SteevenRodriguez/AMSTEcIOT/Documentos Entregables/Diagrama de actividades/Diagrama de actividades HU1.png

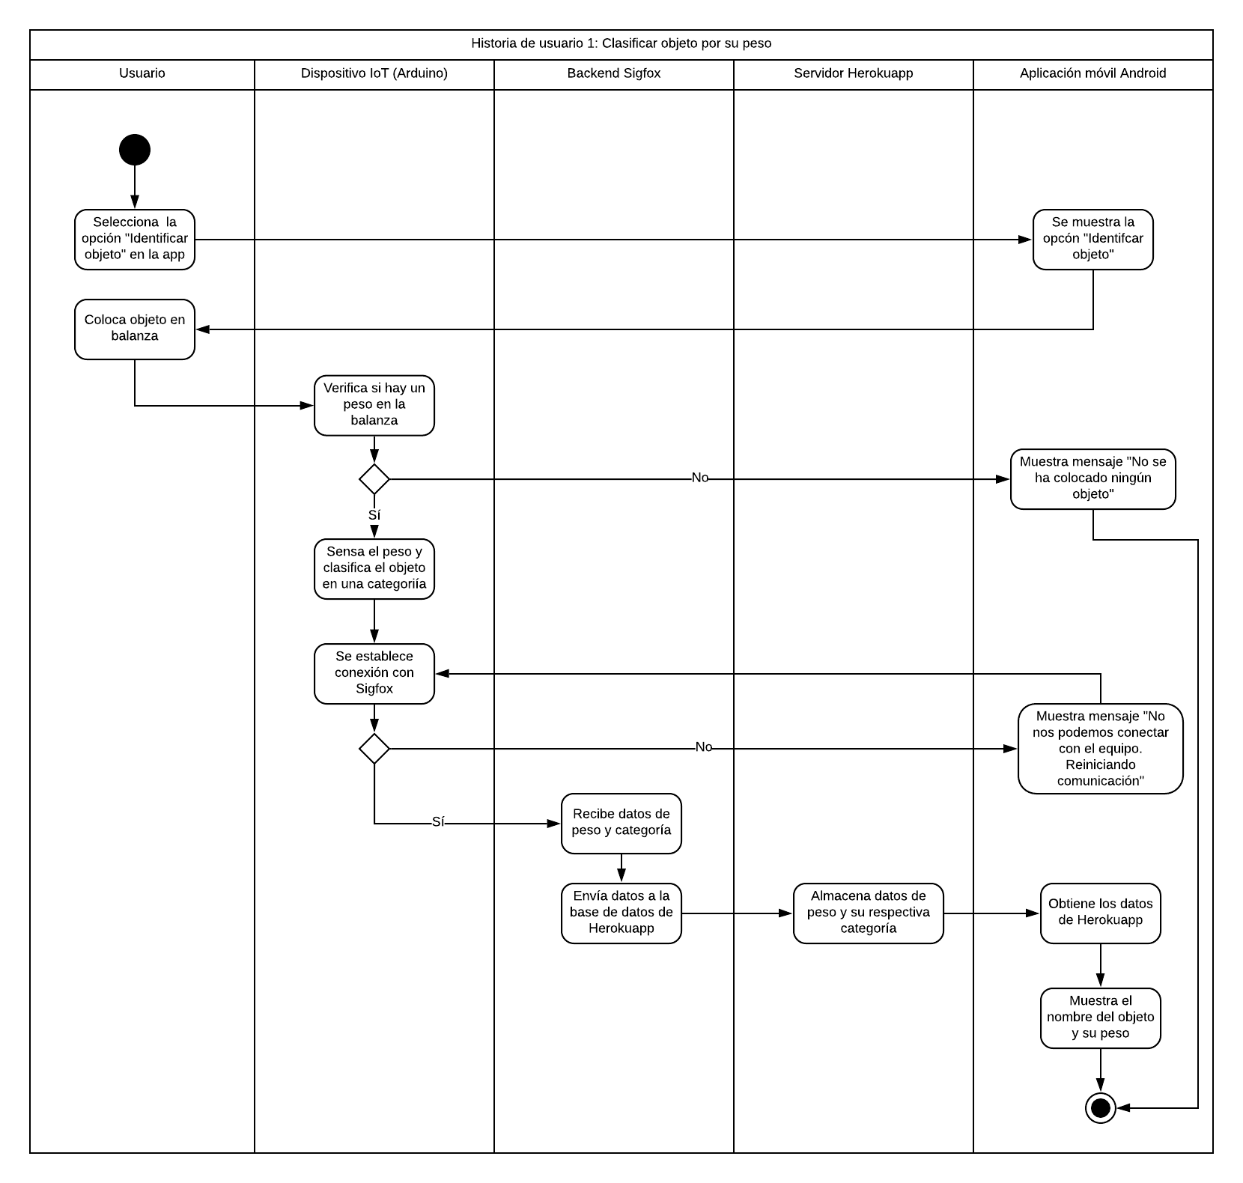
Documentos Entregables/Diagrama de actividades/Diagrama de actividades HU1.png
