SteevenRodriguez/AMSTEcIOT/Documentos Entregables/Diagrama de actividades/Diagrama de actividades HU2.png

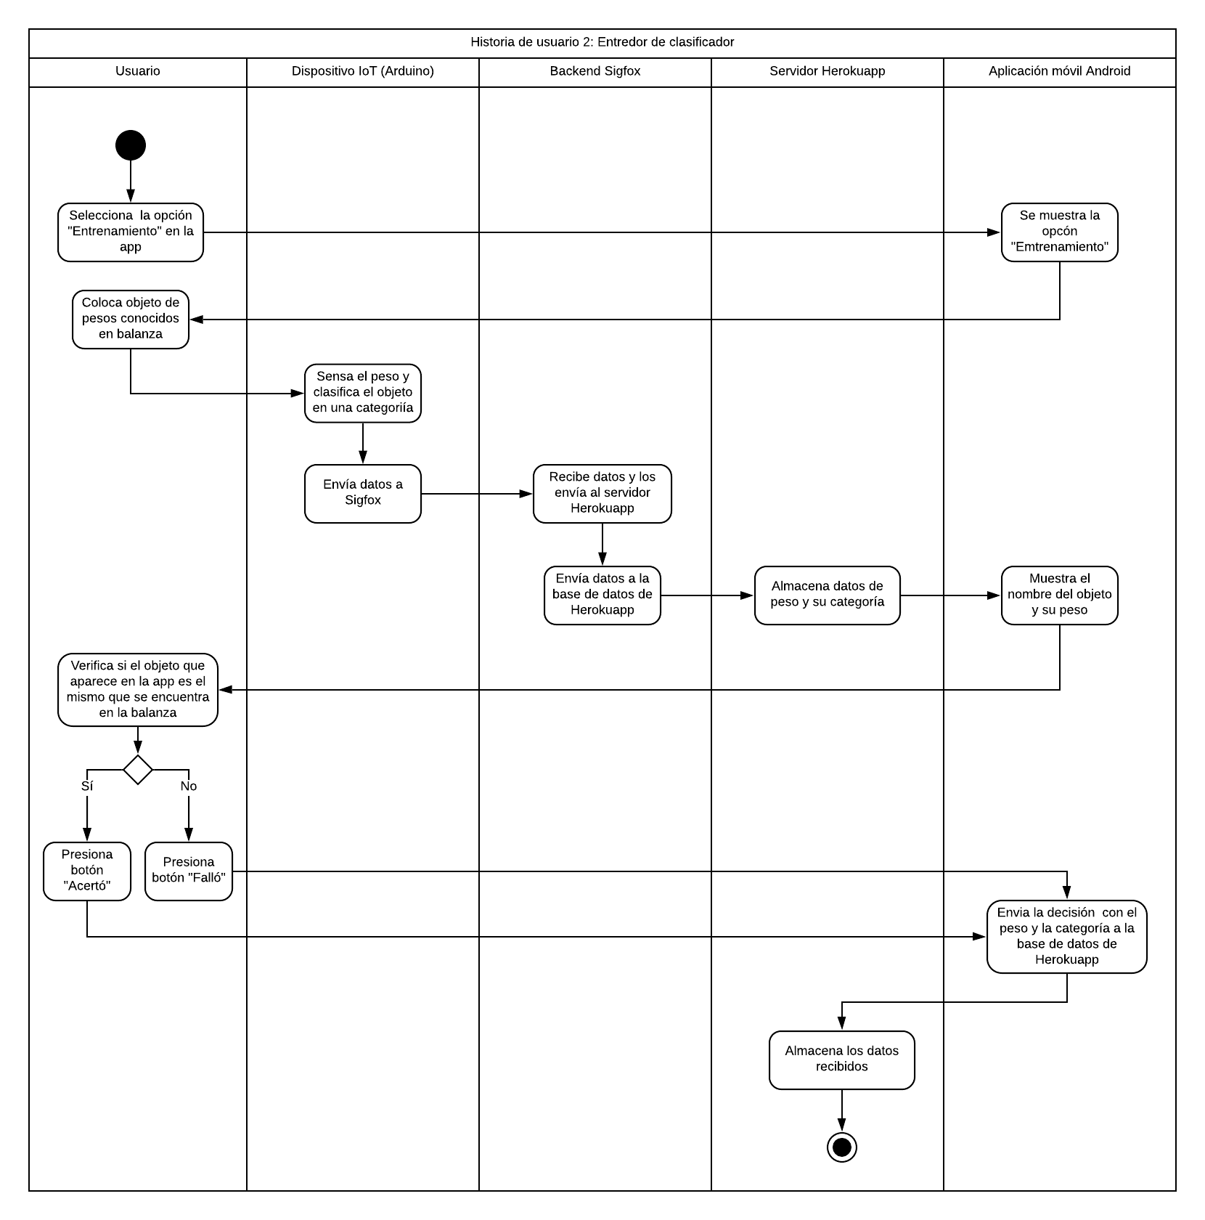
Documentos Entregables/Diagrama de actividades/Diagrama de actividades HU2.png
