SteevenRodriguez/AMSTEcIOT/Documentos Entregables/Diagrama de actividades/Diagrama de actividades HU3.png

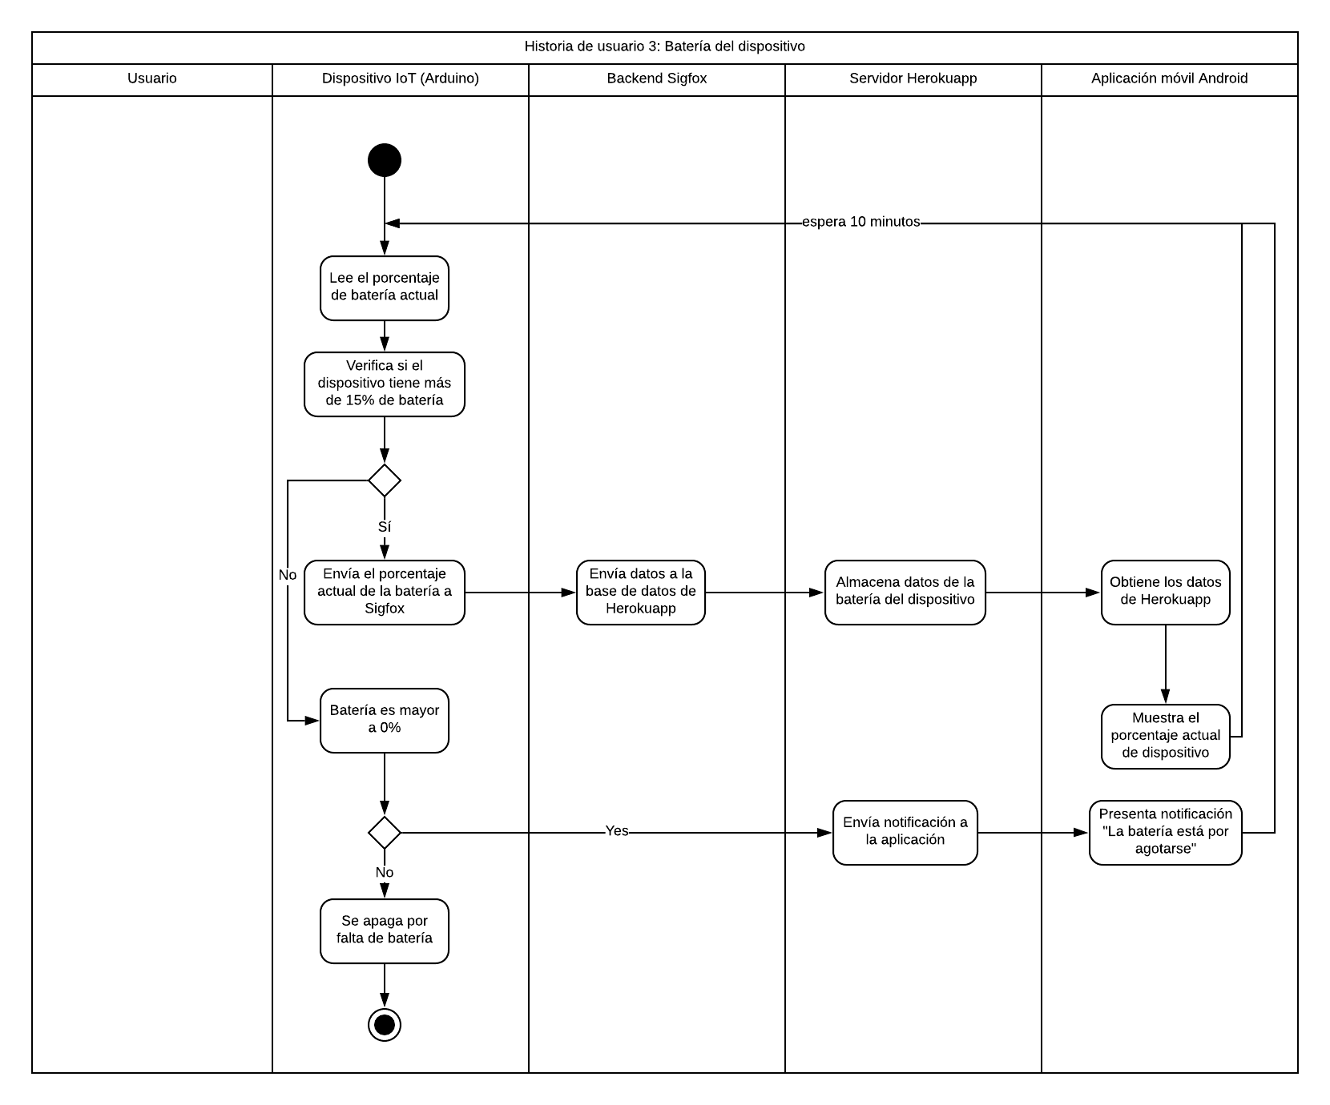
Documentos Entregables/Diagrama de actividades/Diagrama de actividades HU3.png
